rajtik76/weather-station/firmware/weather_station/ca_certs.h

#ifndef CA_CERTS_H
#define CA_CERTS_H

// Roots, never the leaf: Let's Encrypt renews it every couple of months.
// Two on purpose: the server sends ISRG Root YR cross-signed by X1; once the cross-sign
// is dropped, YR keeps working.
// Verified 2026-09-04 against weather.rajtik.com:
//   ISRG Root X1  SHA-256 96:BC:EC:06:26:49:76:F3:74:60:77:9A:CF:28:C5:A7:
//                         CF:E8:A3:C0:AA:E1:1A:8F:FC:EE:05:C0:BD:DF:08:C6
//                 expires 2035-06-04
//   ISRG Root YR  SHA-256 07:26:39:D0:B1:40:D5:BF:FA:E1:6A:D9:C3:F6:CC:60:
//                         86:04:06:21:F5:1E:E6:1A:6D:46:A8:91:5C:07:CF:76
//                 expires 2032-09-02
static const char ROOT_CA_BUNDLE[] = R"CERT(
-----BEGIN CERTIFICATE-----
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
-----END CERTIFICATE-----
-----BEGIN CERTIFICATE-----
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
-----END CERTIFICATE-----
---
Server certificate
subject=CN=weather.rajtik.com
issuer=C=US, O=Let's Encrypt, CN=YR1
---
No client certificate CA names sent
Peer signing digest: SHA256
Peer signature type: rsa_pss_rsae_sha256
Negotiated TLS1.3 group: X25519MLKEM768
---
SSL handshake has read 6210 bytes and written 1613 bytes
Verification: OK
---
New, TLSv1.3, Cipher is TLS_AES_128_GCM_SHA256
Protocol: TLSv1.3
Server public key is 4096 bit
This TLS version forbids renegotiation.
Compression: NONE
Expansion: NONE
No ALPN negotiated
Early data was not sent
Verify return code: 0 (ok)
---
---
Post-Handshake New Session Ticket arrived:
SSL-Session:
    Protocol  : TLSv1.3
    Cipher    : TLS_AES_128_GCM_SHA256
    Session-ID: 26CAAB518F6D5943982B4E00C5CA5633C5C6DC4C3C8EF88B46F825DA7C64205C
    Session-ID-ctx: 
    Resumption PSK: 67DF20D079BA43385721CC4979EEDF4668657D6A10515B89D9CBAD9AAF4B9C80
    PSK identity: None
    PSK identity hint: None
    SRP username: None
    TLS session ticket lifetime hint: 604800 (seconds)
    TLS session ticket:
    0000 - 90 7e 02 43 c5 56 07 86-a2 90 98 6b b0 d5 91 47   .~.C.V.....k...G
    0010 - 4b d8 f1 1f 05 41 f5 b5-5e 54 fa da 66 55 27 38   K....A..^T..fU'8
    0020 - 03 eb c3 0c 1d d8 99 5d-17 17 0b af d9 07 88 5b   .......].......[
    0030 - 86 a0 20 03 f4 04 31 94-bd f1 e6 dd b3 35 1f 3c   .. ...1......5.<
    0040 - 3d 17 b7 e1 8a d8 15 14-c2 05 dd 01 eb bc 8d 50   =..............P
    0050 - 70 f9 e2 95 60 62 50 02-57 d0 58 74 6d ed 2f 0d   p...`bP.W.Xtm./.
    0060 - 2a 4d 90 0c 64 25 23 ee-2d                        *M..d%#.-

    Start Time: 1788521058
    Timeout   : 7200 (sec)
    Verify return code: 0 (ok)
    Extended master secret: no
    Max Early Data: 0
---
read R BLOCK
)CERT";

#endif
