rajtik76/weather-station/firmware/weather_station/transmission_json.h

#ifndef TRANSMISSION_JSON_H
#define TRANSMISSION_JSON_H

#include <ArduinoJson.h>

#include "station_status.h"
#include "transmission_type.h"

// Bytes written excluding the terminator; 0 if the buffer was too small.
static size_t transmissionToJson(const transmission_t& tx, const station_status_t& status,
                                 char* out, size_t outLen) {
  JsonDocument doc;

  doc["sensor_name"] = tx.device;
  doc["protocol_version"] = tx.version;

  JsonArray measurements = doc["measurements"].to<JsonArray>();
  for (uint8_t i = 0; i < tx.data_count; i++) {
    const station_window_t& w = tx.data[i];
    JsonObject entry = measurements.add<JsonObject>();

    // The mean keeps the V1 name so the server aggregates versions alike.
    entry["timestamp"] = w.timestamp;
    entry["temperature"] = w.temperature;
    entry["temperature_min"] = w.temperature_min;
    entry["temperature_max"] = w.temperature_max;
    entry["humidity"] = w.humidity;
    entry["humidity_min"] = w.humidity_min;
    entry["humidity_max"] = w.humidity_max;
    entry["pressure"] = w.pressure;
    entry["pressure_min"] = w.pressure_min;
    entry["pressure_max"] = w.pressure_max;
    entry["samples"] = w.samples;

    // Left out when the VEML7700 gave nothing.
    if (w.illuminance_samples > 0) {
      entry["illuminance"] = w.illuminance;
      entry["illuminance_min"] = w.illuminance_min;
      entry["illuminance_max"] = w.illuminance_max;
    }

    // Left out when the microphone gave nothing.
    if (w.noise.seconds > 0) {
      JsonObject noise = entry["noise"].to<JsonObject>();
      noise["seconds"] = w.noise.seconds;
      noise["laeq"] = w.noise.laeq;
      noise["lamax"] = w.noise.lamax;
      noise["la10"] = w.noise.la10;
      noise["la90"] = w.noise.la90;

      JsonArray bands = noise["bands"].to<JsonArray>();
      for (uint8_t b = 0; b < NOISE_BAND_COUNT; b++) {
        bands.add(w.noise.bands[b]);
      }
    }
  }

  stationStatusToJson(status, doc["station"].to<JsonObject>());

  size_t written = serializeJson(doc, out, outLen);
  return (written > 0 && written < outLen) ? written : 0;
}

#endif
