rajtik76/weather-station/firmware/weather_station/transmission_type.h

#ifndef TRANSMISSION_TYPES_T
#define TRANSMISSION_TYPES_T

#include <stdint.h>

#include "reading_types.h"

// Bump whenever the JSON shape changes.
#define TRANSMISSION_VERSION 4

// The server takes up to 500; 16 keeps the JSON under TRANSMISSION_PAYLOAD_BYTES (~500 bytes per entry with noise).
#define TRANSMISSION_MAX_ENTRIES 16
#define TRANSMISSION_DEVICE_LEN  24
#define TRANSMISSION_PAYLOAD_BYTES 16384

typedef struct {
  uint8_t version;
  char device[TRANSMISSION_DEVICE_LEN];  // e.g. "sensor-001"

  uint8_t data_count;  // valid entries in data[]
  station_window_t data[TRANSMISSION_MAX_ENTRIES];
} transmission_t;

#endif
